wesmith/PID_balance_arm/electronoobs_balance_3D_files/stl/ws-bar.stl

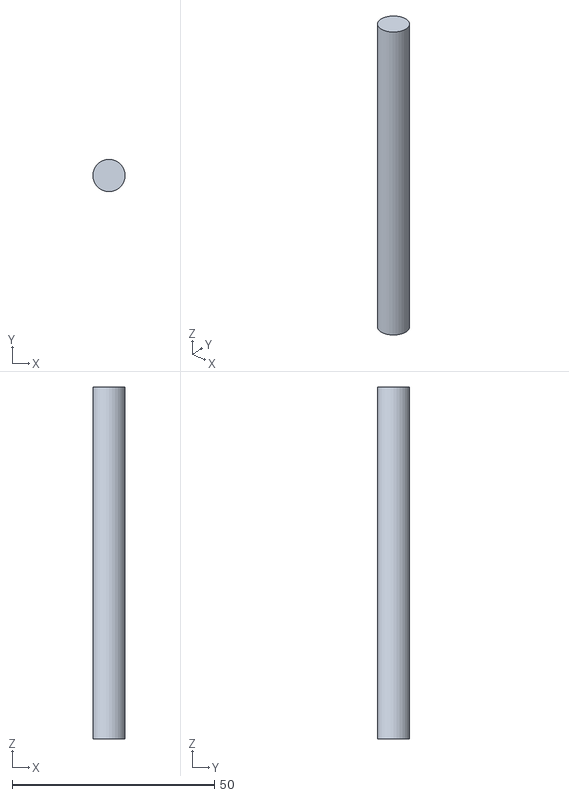
[picture p15: CAD file, 2020-01-23]
electronoobs_balance_3D_files/stl/ws-bar.stl
8.00 x 8.00 x 87.0
