wesmith/PID_balance_arm/electronoobs_balance_3D_files/stl/Small_hinge_2.stl

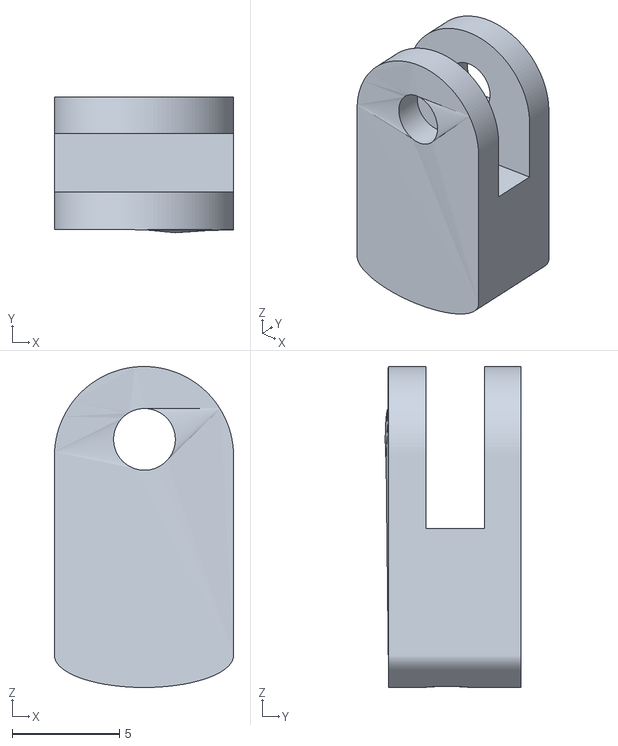
[picture p16: CAD file, 2020-01-23]
electronoobs_balance_3D_files/stl/Small_hinge_2.stl
8.37 x 6.33 x 15.0
