wesmith/PID_balance_arm/electronoobs_balance_3D_files/stl/ws-lever.stl

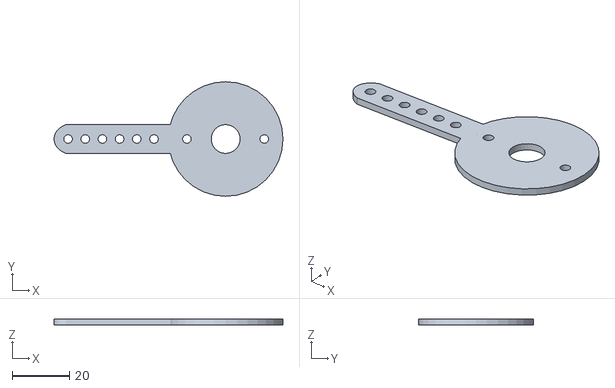
[picture p17: CAD file, 2020-01-23]
electronoobs_balance_3D_files/stl/ws-lever.stl
79.9 x 40.0 x 2.00
