wesmith/PID_balance_arm/electronoobs_balance_3D_files/stl/End_stop.stl

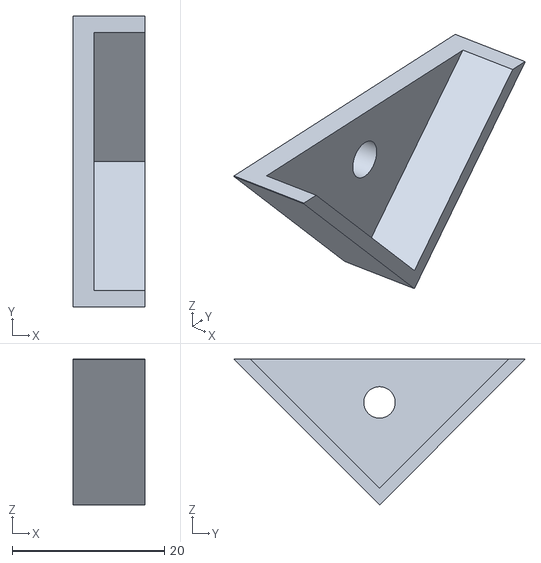
[picture p18: CAD file, 2020-01-23]
electronoobs_balance_3D_files/stl/End_stop.stl
9.42 x 38.2 x 19.2
